terminalwaltz/minichord/documentation/docs/ressources/hero.png

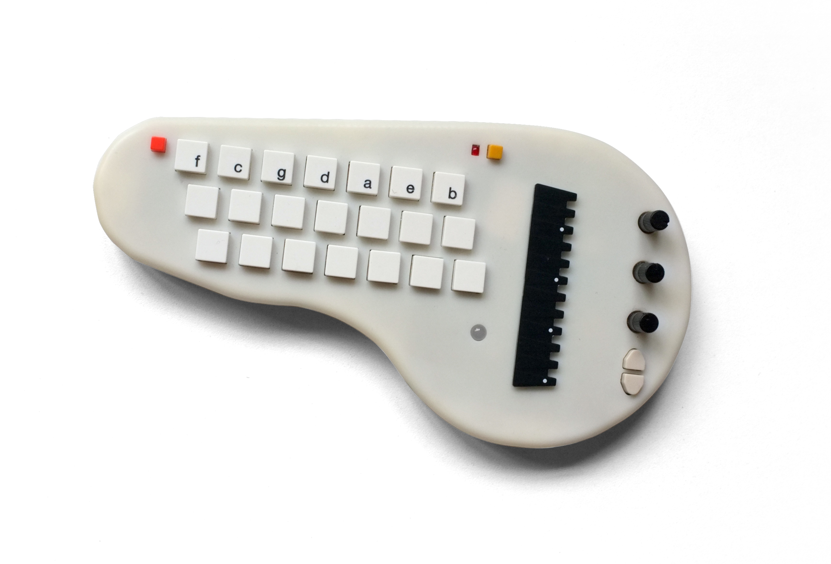
documentation/docs/ressources/hero.png
