terminalwaltz/minichord/hardware/3D/DXF/MiniChord-User_reset_zone.dxf

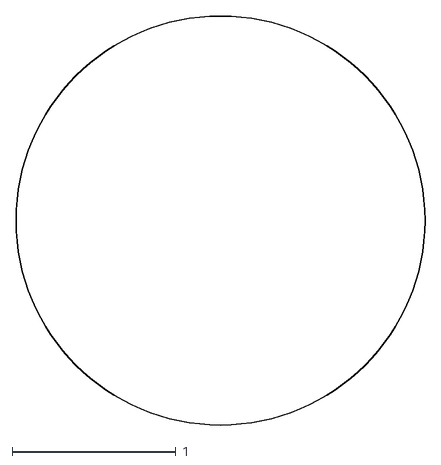
[picture p17: CAD file, 2024-12-26]
hardware/3D/DXF/MiniChord-User_reset_zone.dxf
2.50 x 2.50
