terminalwaltz/minichord/firmware/include/sysex_handler.h

void apply_audio_parameter(int adress, int value) {
    switch(adress){
      case 20:
        bank_led_hue=value; set_led_color(bank_led_hue, 1.0, 1-led_attenuation);
        break;
      case 32:
        led_attenuation=value/100.0; set_led_color(bank_led_hue, 1.0, 1-led_attenuation);
        break;
      case 21:
        retrigger_chord=value;
        break;
      case 22:
        change_held_strings=value;
        break;
      case 23:
        note_slash_level=value;
        break;
      case 30:
        transpose_semitones=value;midi_base_note_transposed=midi_base_note+transpose_semitones;
        break;
      case 31:
        flat_button_modifier=value;
        break;
      case 33:
        barry_harris_mode=value;
        break;
      case 34:
        chord_frame_shift=value;
        break;
      case 35:
        key_signature_selection=value;
        break;
      case 24:
        main_reverb.size(value/100.0);
        break;
      case 25:
        main_reverb.hidamp(value/100.0);
        break;
      case 26:
        main_reverb.lodamp(value/100.0);
        break;
      case 27:
        main_reverb.lowpass(value/100.0);
        break;
      case 28:
        main_reverb.diffusion(value/100.0);
        break;
      case 29:
        pan=value/100.0;apply_audio_parameter(85, current_sysex_parameters[85]);apply_audio_parameter(184, current_sysex_parameters[184]);
        break;
      case 10:
        chord_pot.set_alternate(value);
        break;
      case 11:
        chord_pot.set_alternate_range(value);
        break;
      case 12:
        harp_pot.set_alternate(value);
        break;
      case 13:
        harp_pot.set_alternate_range(value);
        break;
      case 14:
        mod_pot.set_main(value);
        break;
      case 15:
        mod_pot.set_main_range(value);
        break;
      case 16:
        mod_pot.set_alternate(value);
        break;
      case 17:
        mod_pot.set_alternate_range(value);
        break;
      case 4:
        chord_pot.set_alternate_default(value);chord_pot.force_update();
        break;
      case 5:
        harp_pot.set_alternate_default(value);harp_pot.force_update();
        break;
      case 6:
        mod_pot.set_alternate_default(value);mod_pot.force_update();
        break;
      case 7:
        current_sysex_parameters[7]=version_ID;
        break;
      case 2:
        string_gain.amplitude(value/100.0,100);  harp_attack_velocity=value/100.0*127;
        break;
      case 99:
        for (int i=0;i<12;i++){
          harp_octave_change=value; current_harp_notes[i]=calculate_note_harp(i,slash_chord,sharp_active);
        }
        break;
      case 40:
        for (int i=0;i<12;i++){
          harp_shuffling_selection=value; current_harp_notes[i]=calculate_note_harp(i,slash_chord,sharp_active);
        }
        break;
      case 98:
        chromatic_harp_mode=value;
        break;
      case 41:
        for (int i=0;i<12;i++){
          string_waveform_array[i]->amplitude(value/100.0);
        }
        break;
      case 42:
        for (int i=0;i<12;i++){
          string_waveform_array[i]->begin(waveform_array[value]);
        }
        break;
      case 43:
        for (int i=0;i<12;i++){
          string_enveloppe_array[i]->attack(value);
        }
        break;
      case 44:
        for (int i=0;i<12;i++){
          string_enveloppe_array[i]->hold(value);
        }
        break;
      case 45:
        for (int i=0;i<12;i++){
          string_enveloppe_array[i]->decay(value);
        }
        break;
      case 46:
        for (int i=0;i<12;i++){
              string_enveloppe_array[i]->sustain(value/100.0);
        }
        break;
      case 47:
        for (int i=0;i<12;i++){
          string_enveloppe_array[i]->release(value);
        }
        break;
      case 48:
        for (int i=0;i<12;i++){
          string_enveloppe_array[i]->releaseNoteOn(value);
        }
        break;
      case 49:
        string_filter_base_freq=value;
        break;
      case 50:
        string_filter_keytrack=value/100.0;
        break;
      case 51:
        for (int i=0;i<12;i++){
          string_filter_array[i]->resonance(value/100.0);
        }
        break;
      case 52:
        for (int i=0;i<12;i++){
          string_enveloppe_filter_array[i]->attack(value);
        }
        break;
      case 53:
        for (int i=0;i<12;i++){
          string_enveloppe_filter_array[i]->hold(value);
        }
        break;
      case 54:
        for (int i=0;i<12;i++){
          string_enveloppe_filter_array[i]->decay(value);
        }
        break;
      case 55:
        for (int i=0;i<12;i++){
          string_enveloppe_filter_array[i]->sustain(value/100.0);
        }
        break;
      case 56:
        for (int i=0;i<12;i++){
          string_enveloppe_filter_array[i]->release(value);
        }
        break;
      case 57:
        for (int i=0;i<12;i++){
          string_enveloppe_filter_array[i]->releaseNoteOn(value);
        }
        break;
      case 58:
        for (int i=0;i<12;i++){
          string_filter_array[i]->octaveControl(value/100.0);
        }
        break;
      case 100:
        for (int i=0;i<12;i++){
          string_transient_waveform_array[i]->begin(waveform_array[value]);
        }
        break;
      case 101:
        for (int i=0;i<12;i++){
          string_transient_waveform_array[i]->amplitude(value/100.0);
        }
        break;
      case 102:
        for (int i=0;i<12;i++){
          string_transient_envelope_array[i]->attack(value);
        }
        break;
      case 103:
        for (int i=0;i<12;i++){
          string_transient_envelope_array[i]->hold(value);
        }
        break;
      case 104:
        for (int i=0;i<12;i++){
          string_transient_envelope_array[i]->decay(value);string_transient_envelope_array[i]->release(value);
        }
        break;
      case 105:
        transient_note_level=value;
        break;
      case 59:
        string_tremolo_lfo.begin(waveform_array[value]);
        break;
      case 60:
        string_tremolo_lfo.frequency(value/100.0);
        break;
      case 61:
        string_tremolo_lfo.amplitude(0.01+value/100.0);string_tremolo_lfo.offset(1-value/100.0);
        break;
      case 62:
        string_vibrato_lfo.begin(waveform_array[value]);
        break;
      case 63:
        string_vibrato_lfo.frequency(value/100.0);
        break;
      case 64:
        string_vibrato_lfo.amplitude(0.01+value/100.0);
        break;
      case 65:
        envelope_string_vibrato_lfo.attack(value);
        break;
      case 66:
        envelope_string_vibrato_lfo.hold(value);
        break;
      case 67:
        envelope_string_vibrato_lfo.decay(value);
        break;
      case 68:
        envelope_string_vibrato_lfo.sustain(value/100.0);
        break;
      case 69:
        envelope_string_vibrato_lfo.release(value);
        break;
      case 70:
        envelope_string_vibrato_lfo.releaseNoteOn(value);
        break;
      case 71:
        string_vibrato_dc.amplitude(value/100.0-1);
        break;
      case 72:
        envelope_string_vibrato_dc.attack(value);
        break;
      case 73:
        envelope_string_vibrato_dc.hold(value);
        break;
      case 74:
        envelope_string_vibrato_dc.decay(value);
        break;
      case 75:
        envelope_string_vibrato_dc.releaseNoteOn(value);
        break;
      case 76:
        for (int i=0;i<12;i++){
          string_waveform_array[i]->frequencyModulation(value/100.0);
        }
        break;
      case 77:
        delay_strings.delay(0,value);
        break;
      case 78:
        filter_delay_strings.frequency(value);
        break;
      case 79:
        filter_delay_strings.resonance(value/100.0);
        break;
      case 80:
        string_delay_mix.gain(1,value/100.0);
        break;
      case 81:
        string_delay_mix.gain(2,value/100.0);
        break;
      case 82:
        string_delay_mix.gain(3,value/100.0);
        break;
      case 83:
        strings_effect_mix.gain(0,value/100.0);
        break;
      case 84:
        strings_effect_mix.gain(1,value/100.0);
        break;
      case 85:
        reverb_mixer.gain(0,value/100.0);string_r_stereo_gain.amplitude((1-reverb_dry_proportion*value/100.0)*pan,100);string_l_stereo_gain.amplitude(1-reverb_dry_proportion*value/100.0,100);
        break;
      case 86:
        string_waveshaper_mix.gain(0,1-value/100.0);string_waveshaper_mix.gain(1,value/100.0);
        break;
      case 87:
        ws_sin_param=value;calculate_ws_array(); string_waveshape.shape(wave_shape,257);
        break;
      case 88:
        string_filter.frequency(value);
        break;
      case 89:
        string_filter.resonance(value/100.0);
        break;
      case 90:
        string_filter_mixer.gain(0,value/100.0);
        break;
      case 91:
        string_filter_mixer.gain(1,value/100.0);
        break;
      case 92:
        string_filter_mixer.gain(2,value/100.0);
        break;
      case 93:
        string_filter_lfo.begin(waveform_array[value]);
        break;
      case 94:
        string_filter_lfo.frequency(value/100.0);
        break;
      case 95:
        string_filter_lfo.amplitude(value/100.0);
        break;
      case 96:
        string_filter.octaveControl(value/100.0);
        break;
      case 97:
        string_amplifier.gain(value/100.0);
        break;
      case 3:
        chords_gain.amplitude(value/100.0,100); chord_attack_velocity=value/100.0*127;
        break;
      case 120:
        for (int i=0;i<7;i++){
          chord_shuffling_selection=value; current_chord_notes[i]=calculate_note_chord(i,slash_chord,sharp_active);
        }
        break;
      case 198:
        for (int i=0;i<4;i++){
          chord_octave_change=value; current_chord_notes[i]=calculate_note_chord(i,slash_chord,sharp_active);
        }
        break;
      case 121:
        for (int i=0;i<4;i++){
          chord_osc_1_array[i]->amplitude(value/100.0);
        }
        break;
      case 122:
        for (int i=0;i<4;i++){
          chord_osc_1_array[i]->begin(waveform_array[value]);
        }
        break;
      case 123:
        osc_1_freq_multiplier=value/100.0;
        break;
      case 124:
        for (int i=0;i<4;i++){
          chord_osc_2_array[i]->amplitude(value/100.0);
        }
        break;
      case 125:
        for (int i=0;i<4;i++){
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
        break;
      case 195:
        chords_main_filter_mixer.gain(1,value/100.0);
        break;
      case 196:
        chords_main_filter_mixer.gain(2,value/100.0);
        break;
      case 197:
        chords_amplifier.gain(value/100.0);
        break;
  }
}
